JosueAGtz/displayArray/Media/Clock Themes Preview/7Segment.png

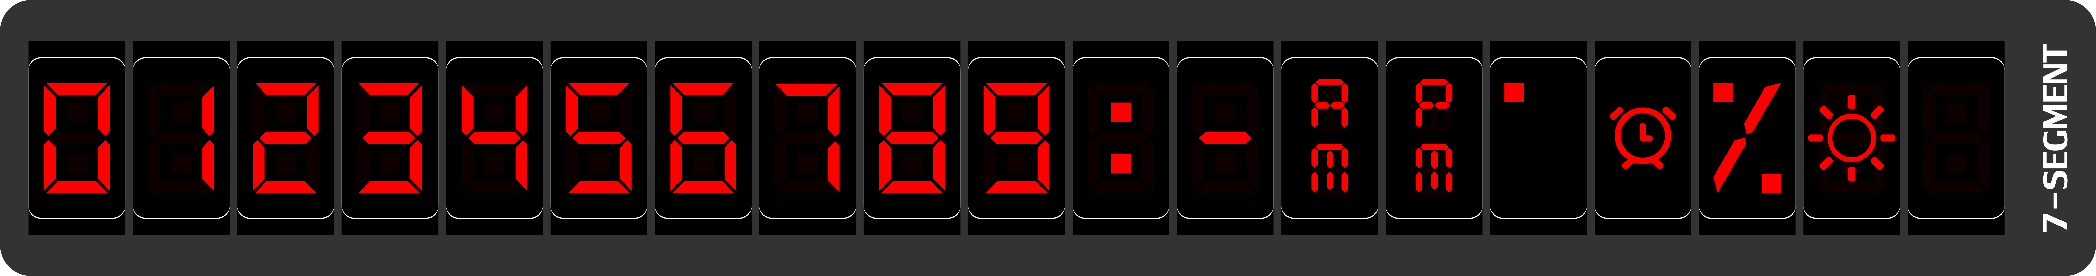
Media/Clock Themes Preview/7Segment.png
