JosueAGtz/displayArray/Media/Clock Themes Preview/14Segment.png

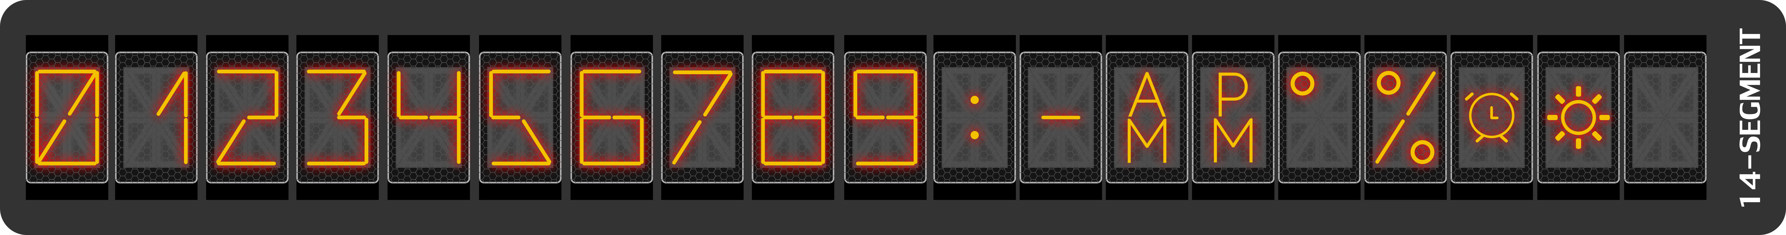
Media/Clock Themes Preview/14Segment.png
