JosueAGtz/displayArray/Media/Clock Themes Preview/BINAView.png

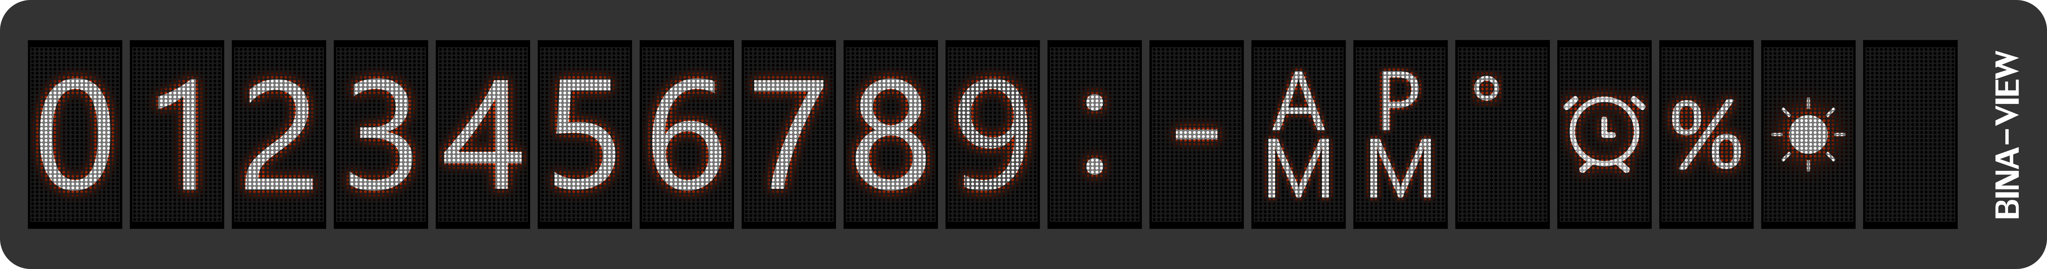
Media/Clock Themes Preview/BINAView.png
