JosueAGtz/displayArray/Media/Clock Themes Preview/Butterfly.png

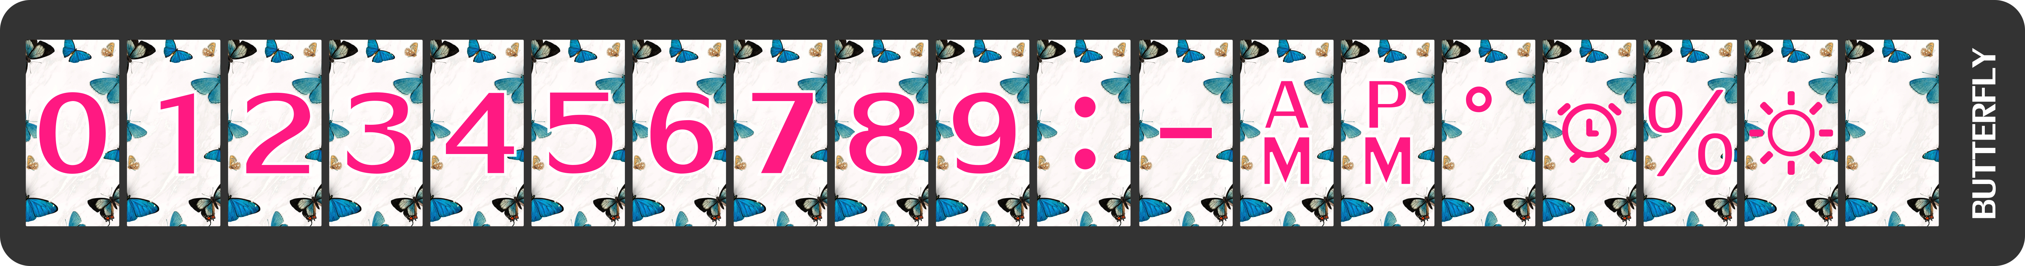
Media/Clock Themes Preview/Butterfly.png
