JosueAGtz/displayArray/Media/Clock Themes Preview/Flowers.png

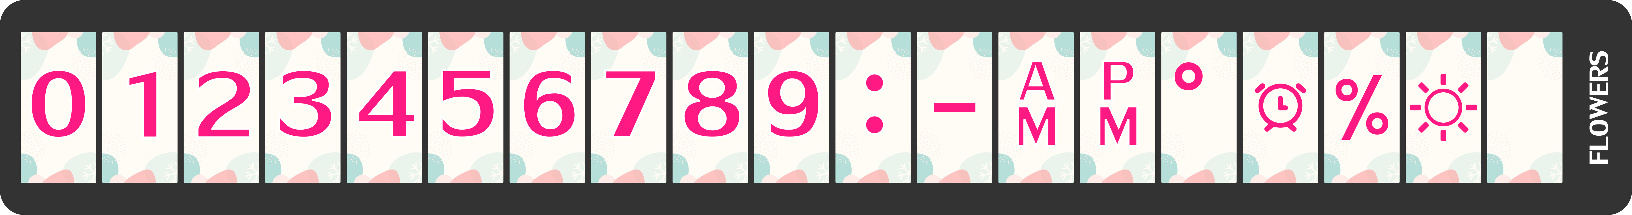
Media/Clock Themes Preview/Flowers.png
