JosueAGtz/displayArray/Media/Clock Themes Preview/LixieBlue.png

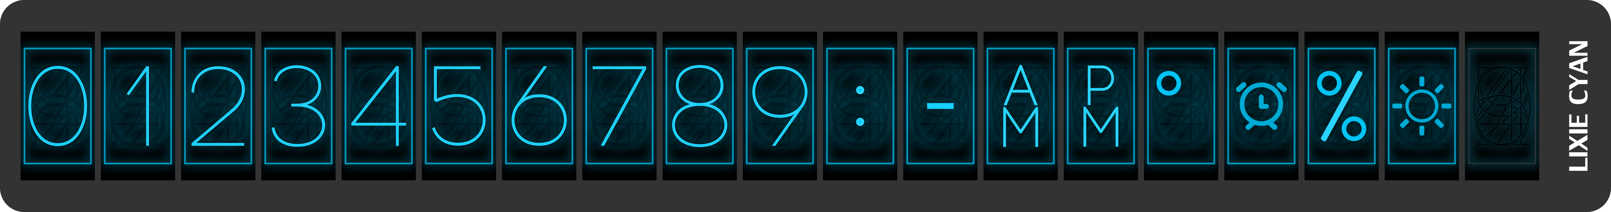
Media/Clock Themes Preview/LixieBlue.png
