JosueAGtz/displayArray/Media/Clock Themes Preview/LixiePurple.png

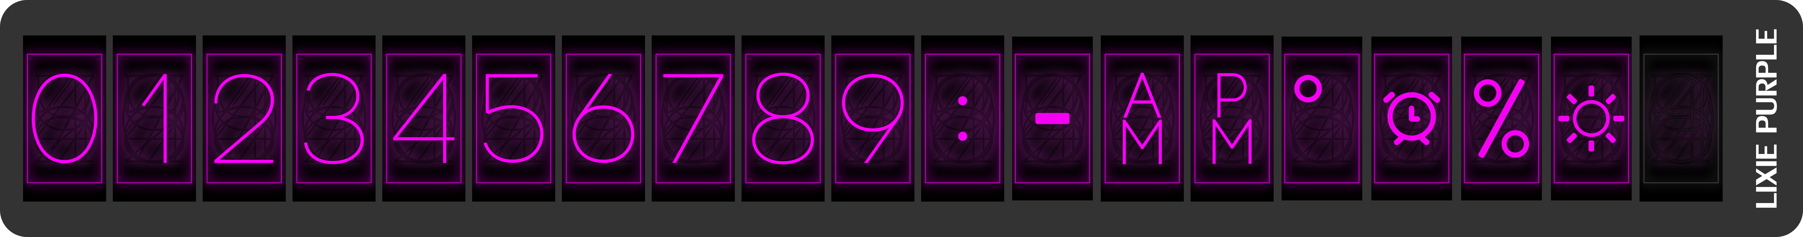
Media/Clock Themes Preview/LixiePurple.png
