JosueAGtz/displayArray/Media/Clock Themes Preview/Matrix.png

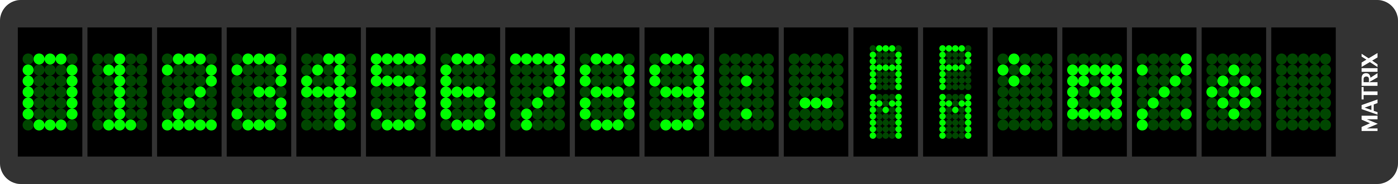
Media/Clock Themes Preview/Matrix.png
