JosueAGtz/displayArray/Media/Clock Themes Preview/NeonBlue.png

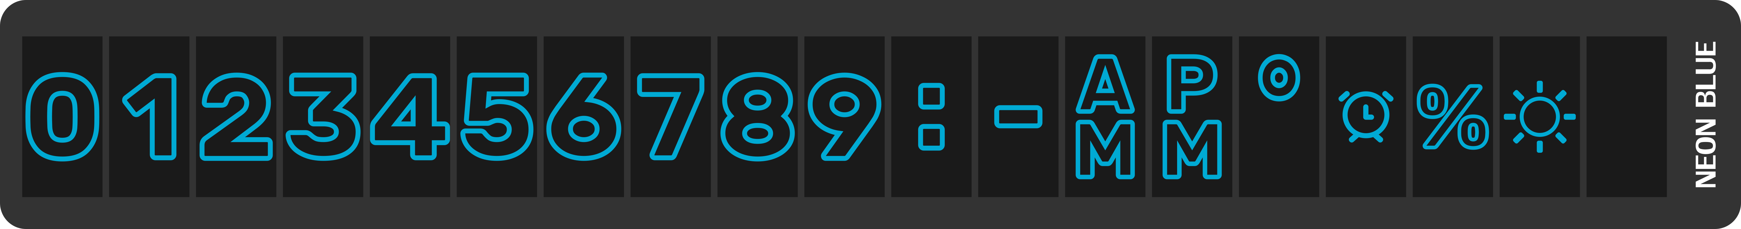
Media/Clock Themes Preview/NeonBlue.png
