JosueAGtz/displayArray/Media/Clock Themes Preview/NeonPurple.png

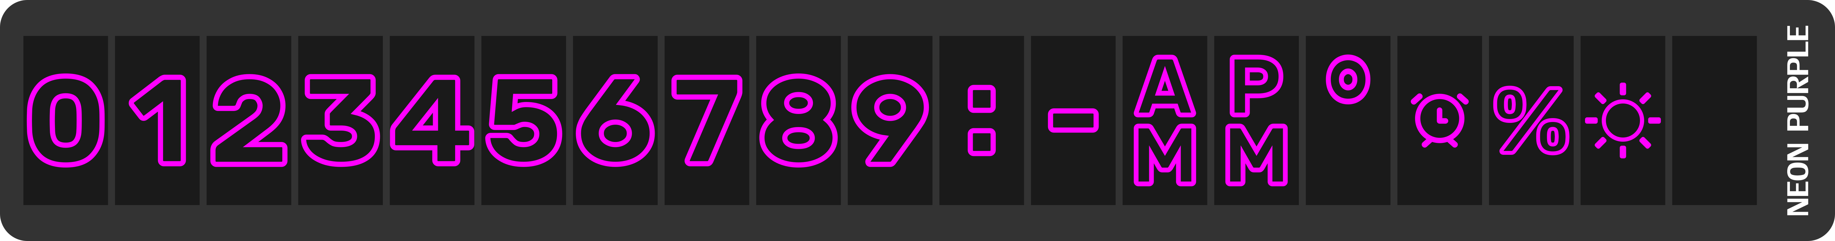
Media/Clock Themes Preview/NeonPurple.png
