JosueAGtz/displayArray/Media/Clock Themes Preview/NIMO.png

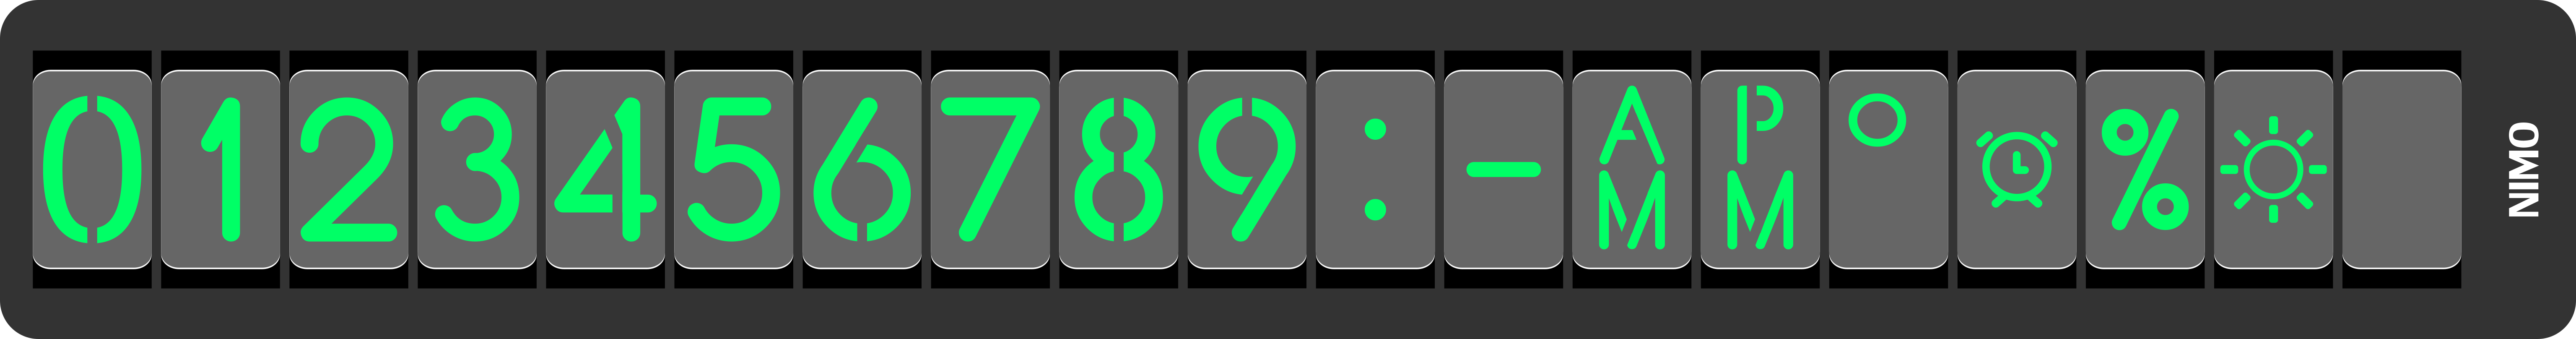
Media/Clock Themes Preview/NIMO.png
