JosueAGtz/displayArray/Media/Clock Themes Preview/PixiePro.png

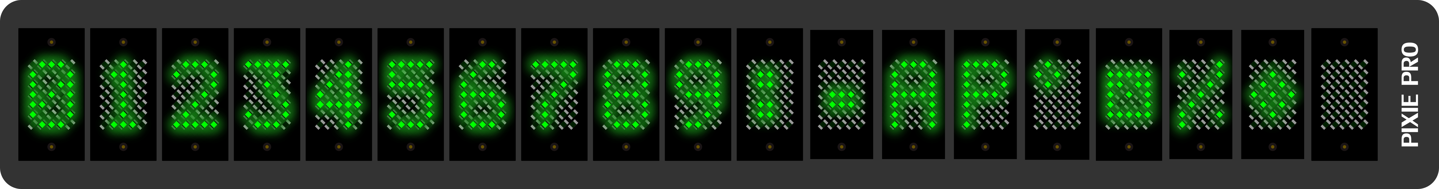
Media/Clock Themes Preview/PixiePro.png
