JosueAGtz/displayArray/Media/Clock Themes Preview/Predator.png

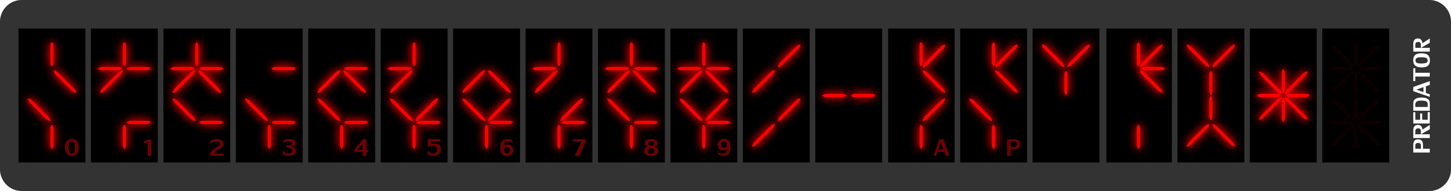
Media/Clock Themes Preview/Predator.png
