JosueAGtz/displayArray/Media/Clock Themes Preview/RGB.png

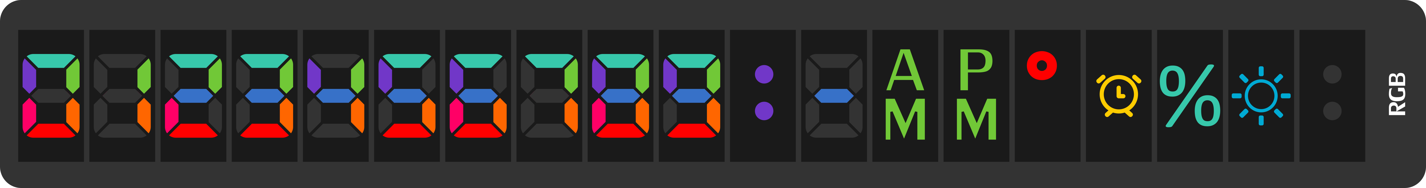
Media/Clock Themes Preview/RGB.png
