JosueAGtz/displayArray/Media/Clock Themes Preview/Stargate.png

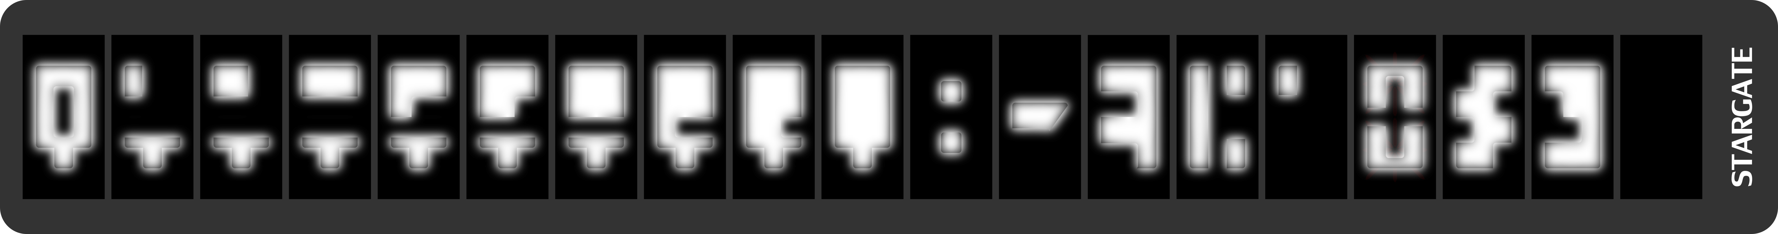
Media/Clock Themes Preview/Stargate.png
