JosueAGtz/displayArray/Media/Clock Themes Preview/VFD.png

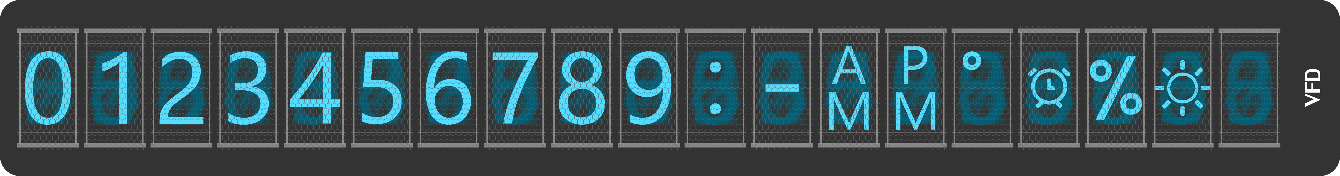
Media/Clock Themes Preview/VFD.png
