JosueAGtz/displayArray/Media/displayArray Plus Themes/7SegmentBig/alarm.png

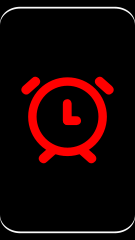
Media/displayArray Plus Themes/7SegmentBig/alarm.png
