JosueAGtz/displayArray/Media/displayArray Plus Themes/7SegmentBig/colon.png

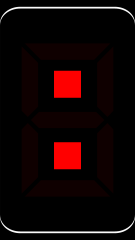
Media/displayArray Plus Themes/7SegmentBig/colon.png
