JosueAGtz/displayArray/Media/displayArray Plus Themes/7SegmentBig/degrees.png

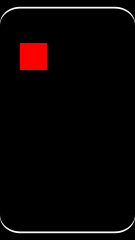
Media/displayArray Plus Themes/7SegmentBig/degrees.png
