JosueAGtz/displayArray/Media/displayArray Plus Themes/14SegmentBig/am.png

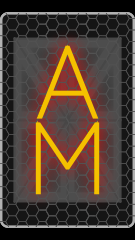
Media/displayArray Plus Themes/14SegmentBig/am.png
