JosueAGtz/displayArray/Media/displayArray Plus Themes/14SegmentBig/brightness.png

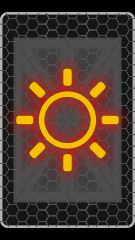
Media/displayArray Plus Themes/14SegmentBig/brightness.png
