JosueAGtz/displayArray/Media/displayArray Plus Themes/14SegmentBig/colon.png

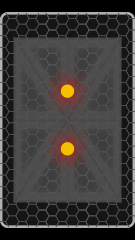
Media/displayArray Plus Themes/14SegmentBig/colon.png
