JosueAGtz/displayArray/Media/displayArray Plus Themes/14SegmentBig/degrees.png

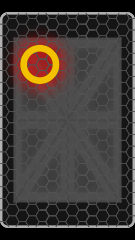
Media/displayArray Plus Themes/14SegmentBig/degrees.png
