JosueAGtz/displayArray/Media/displayArray Plus Themes/14SegmentBig/pm.png

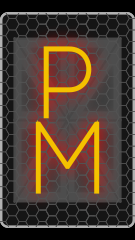
Media/displayArray Plus Themes/14SegmentBig/pm.png
