JosueAGtz/displayArray/Media/displayArray Plus Themes/BINAViewBig/alarm.png

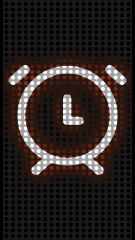
Media/displayArray Plus Themes/BINAViewBig/alarm.png
