JosueAGtz/displayArray/Media/displayArray Plus Themes/BINAViewBig/am.png

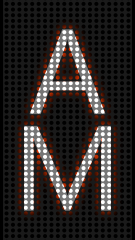
Media/displayArray Plus Themes/BINAViewBig/am.png
