JosueAGtz/displayArray/Media/displayArray Plus Themes/BINAViewBig/brightness.png

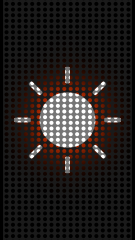
Media/displayArray Plus Themes/BINAViewBig/brightness.png
