JosueAGtz/displayArray/Media/displayArray Plus Themes/BINAViewBig/colon.png

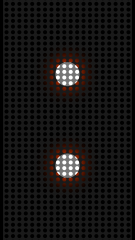
Media/displayArray Plus Themes/BINAViewBig/colon.png
