JosueAGtz/displayArray/Media/displayArray Plus Themes/ButterflyBig/alarm.png

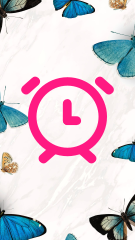
Media/displayArray Plus Themes/ButterflyBig/alarm.png
