JosueAGtz/displayArray/Media/displayArray Plus Themes/ButterflyBig/am.png

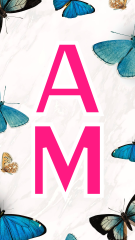
Media/displayArray Plus Themes/ButterflyBig/am.png
