JosueAGtz/displayArray/Media/displayArray Plus Themes/ButterflyBig/colon.png

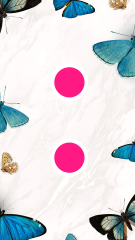
Media/displayArray Plus Themes/ButterflyBig/colon.png
