JosueAGtz/displayArray/Media/displayArray Plus Themes/ButterflyBig/degrees.png

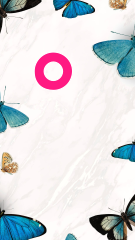
Media/displayArray Plus Themes/ButterflyBig/degrees.png
