JosueAGtz/displayArray/Media/displayArray Plus Themes/FlipFlapBig/alarm.png

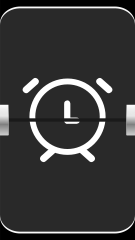
Media/displayArray Plus Themes/FlipFlapBig/alarm.png
