JosueAGtz/displayArray/Media/displayArray Plus Themes/FlipFlapBig/brightness.png

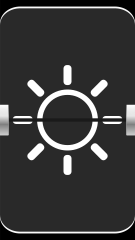
Media/displayArray Plus Themes/FlipFlapBig/brightness.png
