JosueAGtz/displayArray/Media/displayArray Plus Themes/FlipFlapBig/degrees.png

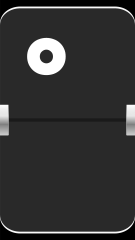
Media/displayArray Plus Themes/FlipFlapBig/degrees.png
