JosueAGtz/displayArray/Media/displayArray Plus Themes/FlowersBig/alarm.png

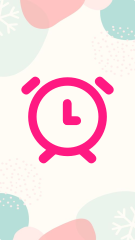
Media/displayArray Plus Themes/FlowersBig/alarm.png
