JosueAGtz/displayArray/Media/displayArray Plus Themes/FlowersBig/am.png

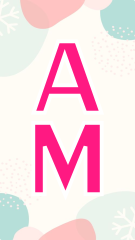
Media/displayArray Plus Themes/FlowersBig/am.png
