JosueAGtz/displayArray/Media/displayArray Plus Themes/FlowersBig/brighthess.png

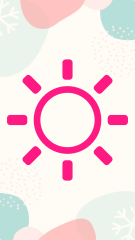
Media/displayArray Plus Themes/FlowersBig/brighthess.png
