JosueAGtz/displayArray/Media/displayArray Plus Themes/FlowersBig/colon.png

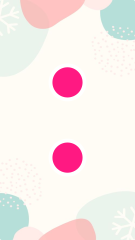
Media/displayArray Plus Themes/FlowersBig/colon.png
