JosueAGtz/displayArray/Media/displayArray Plus Themes/LixieCyanBig/alarm.png

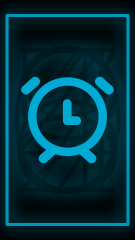
Media/displayArray Plus Themes/LixieCyanBig/alarm.png
