JosueAGtz/displayArray/Media/displayArray Plus Themes/LixieCyanBig/am.png

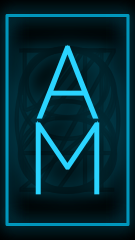
Media/displayArray Plus Themes/LixieCyanBig/am.png
