JosueAGtz/displayArray/Media/displayArray Plus Themes/LixieCyanBig/brightness.png

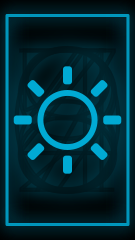
Media/displayArray Plus Themes/LixieCyanBig/brightness.png
