JosueAGtz/displayArray/Media/displayArray Plus Themes/LixieCyanBig/colon.png

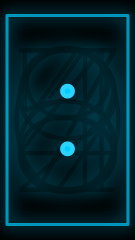
Media/displayArray Plus Themes/LixieCyanBig/colon.png
