JosueAGtz/displayArray/Media/displayArray Plus Themes/LixieCyanBig/degrees.png

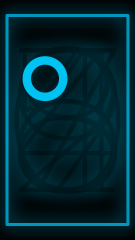
Media/displayArray Plus Themes/LixieCyanBig/degrees.png
