JosueAGtz/displayArray/Media/displayArray Plus Themes/LixieCyanBig/pm.png

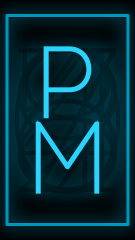
Media/displayArray Plus Themes/LixieCyanBig/pm.png
