JosueAGtz/displayArray/Media/displayArray Plus Themes/LixiePurpleBig/alarm.png

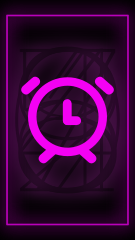
Media/displayArray Plus Themes/LixiePurpleBig/alarm.png
