JosueAGtz/displayArray/Media/displayArray Plus Themes/LixiePurpleBig/brightness.png

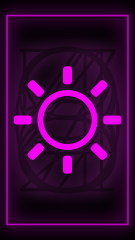
Media/displayArray Plus Themes/LixiePurpleBig/brightness.png
