JosueAGtz/displayArray/Media/displayArray Plus Themes/LixiePurpleBig/degrees.png

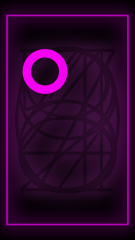
Media/displayArray Plus Themes/LixiePurpleBig/degrees.png
