JosueAGtz/displayArray/Media/displayArray Plus Themes/MatrixBig/am.png

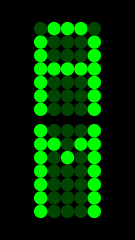
Media/displayArray Plus Themes/MatrixBig/am.png
