JosueAGtz/displayArray/Media/displayArray Plus Themes/MatrixBig/degrees.png

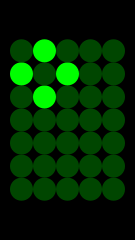
Media/displayArray Plus Themes/MatrixBig/degrees.png
