JosueAGtz/displayArray/Media/displayArray Plus Themes/NeonBlueBig/colon.png

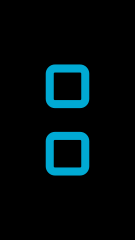
Media/displayArray Plus Themes/NeonBlueBig/colon.png
