JosueAGtz/displayArray/Media/displayArray Plus Themes/NeonBlueBig/degrees.png

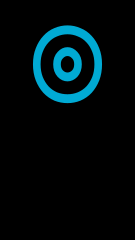
Media/displayArray Plus Themes/NeonBlueBig/degrees.png
