JosueAGtz/displayArray/Media/displayArray Plus Themes/NeonGreenBig/am.png

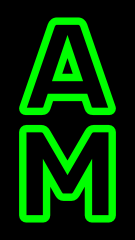
Media/displayArray Plus Themes/NeonGreenBig/am.png
