JosueAGtz/displayArray/Media/displayArray Plus Themes/NeonGreenBig/brightness.png

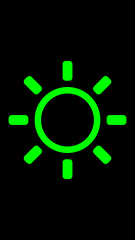
Media/displayArray Plus Themes/NeonGreenBig/brightness.png
