JosueAGtz/displayArray/Media/displayArray Plus Themes/NeonWhiteBig/pm.png

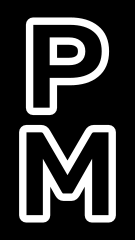
Media/displayArray Plus Themes/NeonWhiteBig/pm.png
