JosueAGtz/displayArray/Media/displayArray Plus Themes/NIMOBig/alarm.png

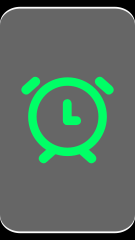
Media/displayArray Plus Themes/NIMOBig/alarm.png
