JosueAGtz/displayArray/Media/displayArray Plus Themes/NIMOBig/brightness.png

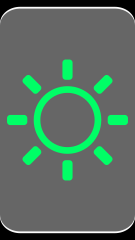
Media/displayArray Plus Themes/NIMOBig/brightness.png
