JosueAGtz/displayArray/Media/displayArray Plus Themes/NIMOBig/colon.png

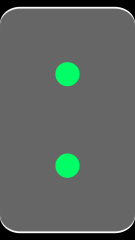
Media/displayArray Plus Themes/NIMOBig/colon.png
