JosueAGtz/displayArray/Media/displayArray Plus Themes/NIMOBig/degrees.png

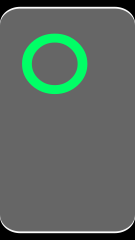
Media/displayArray Plus Themes/NIMOBig/degrees.png
