JosueAGtz/displayArray/Media/displayArray Plus Themes/NIMOBig/pm.png

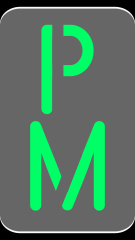
Media/displayArray Plus Themes/NIMOBig/pm.png
