JosueAGtz/displayArray/Media/displayArray Plus Themes/NixieTubeBig/alarm.png

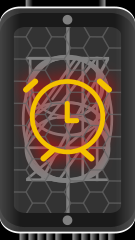
Media/displayArray Plus Themes/NixieTubeBig/alarm.png
