JosueAGtz/displayArray/Media/displayArray Plus Themes/NixieTubeBig/am.png

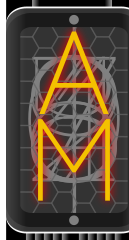
Media/displayArray Plus Themes/NixieTubeBig/am.png
