JosueAGtz/displayArray/Media/displayArray Plus Themes/NixieTubeBig/brightness.png

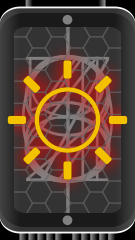
Media/displayArray Plus Themes/NixieTubeBig/brightness.png
