JosueAGtz/displayArray/Media/displayArray Plus Themes/NixieTubeBig/degrees.png

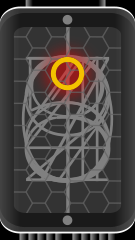
Media/displayArray Plus Themes/NixieTubeBig/degrees.png
