JosueAGtz/displayArray/Media/displayArray Plus Themes/NotebookBig/alarm.png

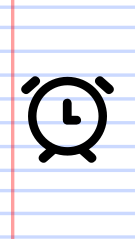
Media/displayArray Plus Themes/NotebookBig/alarm.png
