JosueAGtz/displayArray/Media/displayArray Plus Themes/NotebookBig/am.png

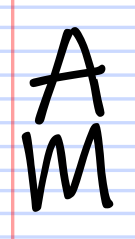
Media/displayArray Plus Themes/NotebookBig/am.png
