JosueAGtz/displayArray/Media/displayArray Plus Themes/NotebookBig/brightness.png

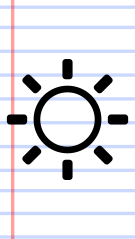
Media/displayArray Plus Themes/NotebookBig/brightness.png
