JosueAGtz/displayArray/Media/displayArray Plus Themes/NotebookBig/degrees.png

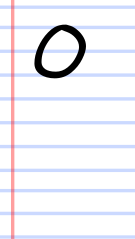
Media/displayArray Plus Themes/NotebookBig/degrees.png
