JosueAGtz/displayArray/Media/displayArray Plus Themes/PixieProBig/alarm.png

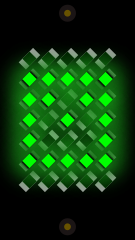
Media/displayArray Plus Themes/PixieProBig/alarm.png
