JosueAGtz/displayArray/Media/displayArray Plus Themes/PixieProBig/am.png

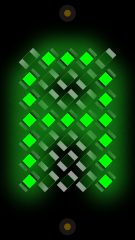
Media/displayArray Plus Themes/PixieProBig/am.png
