JosueAGtz/displayArray/Media/displayArray Plus Themes/PixieProBig/brightness.png

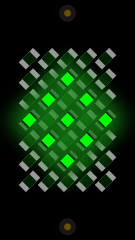
Media/displayArray Plus Themes/PixieProBig/brightness.png
