JosueAGtz/displayArray/Media/displayArray Plus Themes/PixieProBig/colon.png

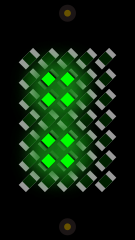
Media/displayArray Plus Themes/PixieProBig/colon.png
