JosueAGtz/displayArray/Media/displayArray Plus Themes/PixieProBig/degrees.png

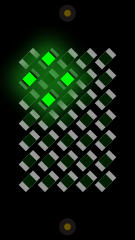
Media/displayArray Plus Themes/PixieProBig/degrees.png
