JosueAGtz/displayArray/Media/displayArray Plus Themes/PixieProBig/pm.png

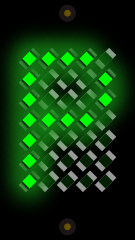
Media/displayArray Plus Themes/PixieProBig/pm.png
