JosueAGtz/displayArray/Media/displayArray Plus Themes/PredatorBig/alarm.png

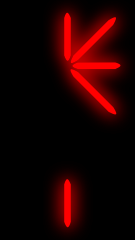
Media/displayArray Plus Themes/PredatorBig/alarm.png
