JosueAGtz/displayArray/Media/displayArray Plus Themes/PredatorBig/am.png

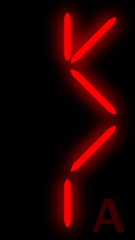
Media/displayArray Plus Themes/PredatorBig/am.png
