JosueAGtz/displayArray/Media/displayArray Plus Themes/PredatorBig/degrees.png

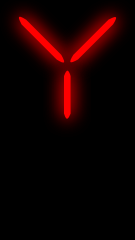
Media/displayArray Plus Themes/PredatorBig/degrees.png
