JosueAGtz/displayArray/Media/displayArray Plus Themes/PredatorBig/pm.png

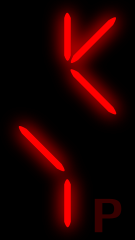
Media/displayArray Plus Themes/PredatorBig/pm.png
