JosueAGtz/displayArray/Media/displayArray Plus Themes/RGBBig/am.png

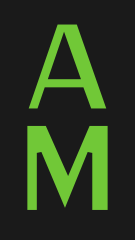
Media/displayArray Plus Themes/RGBBig/am.png
