JosueAGtz/displayArray/Media/displayArray Plus Themes/RGBBig/colon.png

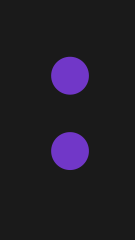
Media/displayArray Plus Themes/RGBBig/colon.png
