JosueAGtz/displayArray/Media/displayArray Plus Themes/RGBBig/degrees.png

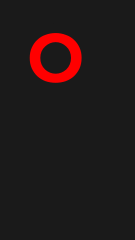
Media/displayArray Plus Themes/RGBBig/degrees.png
