JosueAGtz/displayArray/Media/displayArray Plus Themes/SolidBlueBig/alarm.png

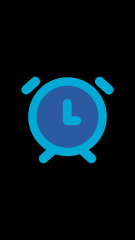
Media/displayArray Plus Themes/SolidBlueBig/alarm.png
