JosueAGtz/displayArray/Media/displayArray Plus Themes/SolidBlueBig/brightness.png

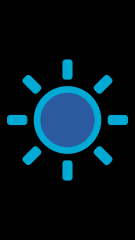
Media/displayArray Plus Themes/SolidBlueBig/brightness.png
