JosueAGtz/displayArray/Media/displayArray Plus Themes/SolidGreenBig/am.png

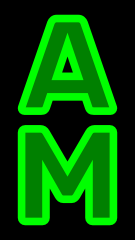
Media/displayArray Plus Themes/SolidGreenBig/am.png
