JosueAGtz/displayArray/Media/displayArray Plus Themes/SolidGreenBig/degrees.png

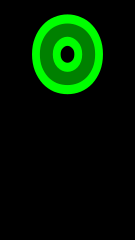
Media/displayArray Plus Themes/SolidGreenBig/degrees.png
