JosueAGtz/displayArray/Media/displayArray Plus Themes/SolidGreenBig/pm.png

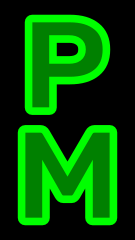
Media/displayArray Plus Themes/SolidGreenBig/pm.png
