JosueAGtz/displayArray/Media/displayArray Plus Themes/SolidYellowBig/am.png

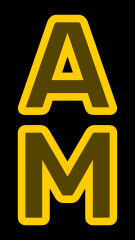
Media/displayArray Plus Themes/SolidYellowBig/am.png
