JosueAGtz/displayArray/Media/displayArray Plus Themes/StargateBig/alarm.png

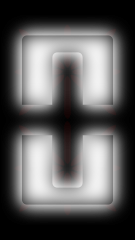
Media/displayArray Plus Themes/StargateBig/alarm.png
