JosueAGtz/displayArray/Media/displayArray Plus Themes/StargateBig/colon.png

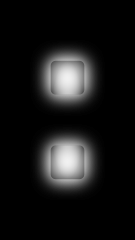
Media/displayArray Plus Themes/StargateBig/colon.png
