JosueAGtz/displayArray/Media/displayArray Plus Themes/StargateBig/degrees.png

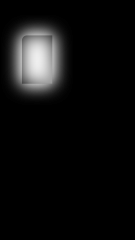
Media/displayArray Plus Themes/StargateBig/degrees.png
