JosueAGtz/displayArray/Media/displayArray Plus Themes/StargateBig/pm.png

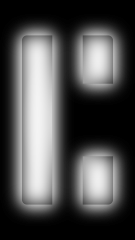
Media/displayArray Plus Themes/StargateBig/pm.png
