JosueAGtz/displayArray/Media/displayArray Plus Themes/VFDBig/alarm.png

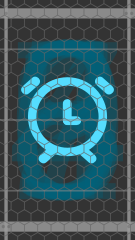
Media/displayArray Plus Themes/VFDBig/alarm.png
