JosueAGtz/displayArray/Media/displayArray Plus Themes/VFDBig/am.png

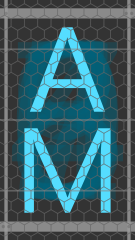
Media/displayArray Plus Themes/VFDBig/am.png
