JosueAGtz/displayArray/Media/displayArray Plus Themes/VFDBig/brightness.png

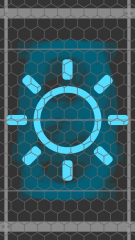
Media/displayArray Plus Themes/VFDBig/brightness.png
