JosueAGtz/displayArray/Media/displayArray Plus Themes/VFDBig/colon.png

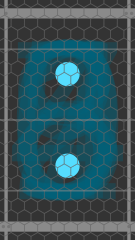
Media/displayArray Plus Themes/VFDBig/colon.png
