JosueAGtz/displayArray/Media/displayArray Plus Themes/VFDBig/degrees.png

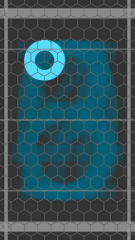
Media/displayArray Plus Themes/VFDBig/degrees.png
