JosueAGtz/displayArray/Media/displayArray Plus Themes/WoodBig/brightness.png

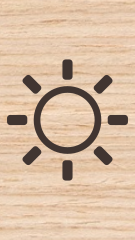
Media/displayArray Plus Themes/WoodBig/brightness.png
