JosueAGtz/displayArray/Media/displayArray Plus Themes/WoodBig/colon.png

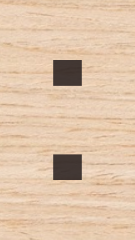
Media/displayArray Plus Themes/WoodBig/colon.png
